qemu-gazebo-sim/pioneer_2DX-Interface/docs/D_NQ_NP_2X_858012-MLB78559910960_082024-F.webp

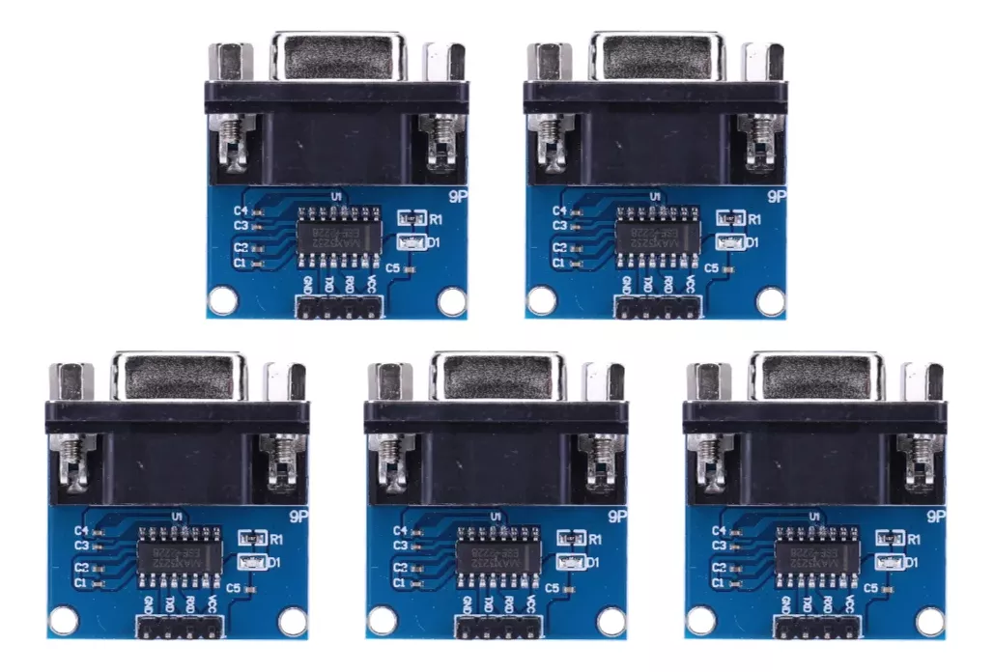
docs/D_NQ_NP_2X_858012-MLB78559910960_082024-F.webp
