qemu-gazebo-sim/pioneer_2DX-Interface/code-esp32_d1/test/test_bluepill_comm.cpp

#include <Arduino.h>
#include <HardwareSerial.h>
#include "bluepill_comm.hpp"
#include <ArduinoLog.h>

HardwareSerial             debug_serial(0);
BluepillCommunication*     bluepill_comm;
nav_msgs::ros_p2os_data_t* mock_p2os_data;
uint32_t                   print_time;

void setup() {
    debug_serial.begin(9600);
    debug_serial.flush();

    Log.begin(LOG_LEVEL_INFO, &debug_serial);

    bluepill_comm = new BluepillCommunication();
    mock_p2os_data = new nav_msgs::ros_p2os_data_t();

    debug_serial.println("Ready!");
    print_time = millis();
}

void loop() {
    bluepill_comm->loop();
    bluepill_comm->send_bluepill_connection(CONNECTED);
    if ((millis() - print_time) > 500) {
        geometry_msgs::Twist current_vel = bluepill_comm->get_velocity();
        MotorSpeed           current_motors_speed = bluepill_comm->get_each_motor_speed();
        ConnectionStates     connection = bluepill_comm->is_bluepill_connected();

        debug_serial.printf(
            "Left: %d | Right: %d |  Linear: %lf |  Angular: %lf | Connection: %d\n", current_motors_speed.left,
            current_motors_speed.right, current_vel.linear.x, current_vel.angular.z, connection
        );

        print_time = millis();
    }

    mock_p2os_data->position.pose.pose.position.x = 10;
    mock_p2os_data->position.pose.pose.position.y = 5;
    mock_p2os_data->sonar.ranges_count = 8;
    mock_p2os_data->sonar.ranges = {0, 1, 2, 3, 4, 5, 6, 7};
    bluepill_comm->update_p2dx_data(*mock_p2os_data);
}
